f-zhuk/Gear-indicator/Headunit/SW_Headunit/ST7735/ST7735.c

#include "ST7735.h"

#include <limits.h>

#include "main.h"

enum ST7735_STATE_ENUM
{
  ST7735_IDLE,
  ST7735_REDRAW
};

uint8_t _st7735_state = ST7735_IDLE;
uint8_t _colstart = 0;   ///< Some displays need this changed to offset
uint8_t _rowstart = 0;   ///< Some displays need this changed to offset
uint8_t _xstart = 0;
uint8_t _ystart = 0;
uint8_t _height = 0;
uint8_t _width = 0;

bool redraw_busy = false;
uint8_t _redraw_xstart = 0;
uint8_t _redraw_ystart = 0;
uint8_t _redraw_xstop = 0;
uint8_t _redraw_ystop = 0;
uint16_t* _redraw_palette;

// Regular grayscale
const uint16_t st7735_palette[16] = 
{
  0x0000,
  0x0111,
  0x0222,
  0x0333,
  0x0444,
  0x0555,
  0x0666,
  0x0777,
  0x0888,
  0x0999,
  0x0AAA,
  0x0BBB,
  0x0CCC,
  0x0DDD,
  0x0EEE,
  0x0FFF
};

const uint16_t st7735_palette_red[16] = 
{
  0x0000,
  0x0100,
  0x0200,
  0x0300,
  0x0400,
  0x0500,
  0x0600,
  0x0700,
  0x0800,
  0x0811,
  0x0911,
  0x0A21,
  0x0B21,
  0x0C22,
  0x0D22,
  0x0E32
};

const uint16_t st7735_palette_green[16] = 
{
  0x0000,
  0x0111,
  0x0222,
  0x0333,
  0x0444,
  0x0555,
  0x0666,
  0x0777,
  0x0888,
  0x0999,
  0x0AAA,
  0x0BBB,
  0x0CCC,
  0x0DDD,
  0x0EEE,
  0x0FFF
};

const uint16_t st7735_palette_rgbi[16] = 
{
  0x0000,
  0x000A,
  0x00A0,
  0x00AA,
  0x0A00,
  0x0A0A,
  0x0A50,
  0x0AAA,
  0x0555,
  0x055F,
  0x05F5,
  0x05FF,
  0x0F55,
  0x0F5F,
  0x0FF5,
  0x0FFF
};

uint8_t st7735_buffer[ST7735_BUFFER];

SPI_HandleTypeDef *ST7735_SPI;

// SCREEN INITIALIZATION ***************************************************

static const uint8_t Rcmd1[] = {                       // 7735R init, part 1 (red or green tab)
    15,                             // 15 commands in list:
    ST77XX_SWRESET,   ST_CMD_DELAY, //  1: Software reset, 0 args, w/delay
      150,                          //     150 ms delay
    ST77XX_SLPOUT,    ST_CMD_DELAY, //  2: Out of sleep mode, 0 args, w/delay
      255,                          //     500 ms delay
    ST7735_FRMCTR1, 3,              //  3: Framerate ctrl - normal mode, 3 arg:
      0x01, 0x2C, 0x2D,             //     Rate = fosc/(1x2+40) * (LINE+2C+2D)
    ST7735_FRMCTR2, 3,              //  4: Framerate ctrl - idle mode, 3 args:
      0x01, 0x2C, 0x2D,             //     Rate = fosc/(1x2+40) * (LINE+2C+2D)
    ST7735_FRMCTR3, 6,              //  5: Framerate - partial mode, 6 args:
      0x01, 0x2C, 0x2D,             //     Dot inversion mode
      0x01, 0x2C, 0x2D,             //     Line inversion mode
    ST7735_INVCTR,  1,              //  6: Display inversion ctrl, 1 arg:
      0x07,                         //     No inversion
    ST7735_PWCTR1,  3,              //  7: Power control, 3 args, no delay:
      0xA2,
      0x02,                         //     -4.6V
      0x84,                         //     AUTO mode
    ST7735_PWCTR2,  1,              //  8: Power control, 1 arg, no delay:
      0xC5,                         //     VGH25=2.4C VGSEL=-10 VGH=3 * AVDD
    ST7735_PWCTR3,  2,              //  9: Power control, 2 args, no delay:
      0x0A,                         //     Opamp current small
      0x00,                         //     Boost frequency
    ST7735_PWCTR4,  2,              // 10: Power control, 2 args, no delay:
      0x8A,                         //     BCLK/2,
      0x2A,                         //     opamp current small & medium low
    ST7735_PWCTR5,  2,              // 11: Power control, 2 args, no delay:
      0x8A, 0xEE,
    ST7735_VMCTR1,  1,              // 12: Power control, 1 arg, no delay:
      0x0E,
    ST77XX_INVOFF,  0,              // 13: Don't invert display, no args
    ST77XX_MADCTL,  1,              // 14: Mem access ctl (directions), 1 arg:
      0xC8,                         //     row/col addr, bottom-top refresh
    ST77XX_COLMOD,  1,              // 15: set color mode, 1 arg, no delay:
      0x03 };                       //     16-bit color

static const uint8_t Rcmd2green160x80[] = {            // 7735R init, part 2 (mini 160x80)
    2,                              //  2 commands in list:
    ST77XX_CASET,   4,              //  1: Column addr set, 4 args, no delay:
      0x00, ST7735_XOFFSET,                   //     XSTART = 26
      0x00, ST7735_WIDTH-1+ST7735_XOFFSET,      //     XEND = 79
    ST77XX_RASET,   4,              //  2: Row addr set, 4 args, no delay:
      0x00, ST7735_YOFFSET,                   //     XSTART = 0
      0x00, ST7735_HEIGHT-1+ST7735_YOFFSET };   //     XEND = 159

static const uint8_t Rcmd3[] = {                       // 7735R init, part 3 (red or green tab)
    4,                              //  4 commands in list:
    ST7735_GMCTRP1, 16      ,       //  1: Gamma Adjustments (pos. polarity), 16 args + delay:
      0x02, 0x1c, 0x07, 0x12,       //     (Not entirely necessary, but provides
      0x37, 0x32, 0x29, 0x2d,       //      accurate colors)
      0x29, 0x25, 0x2B, 0x39,
      0x00, 0x01, 0x03, 0x10,
    ST7735_GMCTRN1, 16      ,       //  2: Gamma Adjustments (neg. polarity), 16 args + delay:
      0x03, 0x1d, 0x07, 0x06,       //     (Not entirely necessary, but provides
      0x2E, 0x2C, 0x29, 0x2D,       //      accurate colors)
      0x2E, 0x2E, 0x37, 0x3F,
      0x00, 0x00, 0x02, 0x10,
    ST77XX_NORON,     ST_CMD_DELAY, //  3: Normal display on, no args, w/delay
      10,                           //     10 ms delay
    ST77XX_DISPOFF,    ST_CMD_DELAY, //  4: Main screen turn on, no args w/delay
      100 };                        //     100 ms delay

void sendCallback(SPI_HandleTypeDef *hspi)
{
  static uint8_t st7735_linebuffer[ST7735_WIDTH*3/2];
  static uint8_t column = 0;
  static uint8_t line = 0;
  static uint16_t bitcounter = 0;
  uint16_t color = 0;

  if(line > _redraw_ystop)
  {
    line = 0;
    column = 0;
    bitcounter = 0;
    HAL_GPIO_WritePin(ST7735_CS_PIN, GPIO_PIN_SET);
    redraw_busy = false;
    return;
  }
  if(line == 0)
  {
    column = _redraw_xstart;
    line = _redraw_ystart;
  }

  HAL_GPIO_WritePin(ST7735_DC_PIN, GPIO_PIN_SET);

  while((bitcounter<960) && (line<=_redraw_ystop)) // Filling 120-byte buffer
  {
    color = _redraw_palette[( st7735_buffer[(line*ST7735_WIDTH+column)>>1] >> ((~(line*ST7735_WIDTH+column)&1)<<2) )&0x0F]; // each byte contains info about 2 pixels, so index increments twice as slow. Checking high nibble first
    st7735_linebuffer[bitcounter>>3]      &= 0xF00>>(bitcounter&0x04); // no shift for even, >>4 for odd
    st7735_linebuffer[(bitcounter>>3)+1]  &= 0x00F>>(bitcounter&0x04); // no shift for even, >>4 for odd

    if (bitcounter&0x07)
    {
      st7735_linebuffer[bitcounter>>3]      |= color>>8;
      st7735_linebuffer[(bitcounter>>3)+1]  |= color;
    }
    else
    {
      st7735_linebuffer[bitcounter>>3]      |= color>>4;
      st7735_linebuffer[(bitcounter>>3)+1]  |= color<<4;
    }

    bitcounter+=12;
    column++;

    if (column > _redraw_xstop)
    {
      column = _redraw_xstart;
      line++;
    }
  }
  
  HAL_SPI_Transmit_IT(hspi, st7735_linebuffer, bitcounter>>3);
  bitcounter = 0;
}

void sendCommandData(uint8_t cmd, const uint8_t *addr, uint16_t numArgs)
{
  HAL_GPIO_WritePin(ST7735_CS_PIN, GPIO_PIN_RESET);
  HAL_GPIO_WritePin(ST7735_DC_PIN, GPIO_PIN_RESET);
  HAL_SPI_Transmit(ST7735_SPI, &cmd, 1, 100);
  HAL_GPIO_WritePin(ST7735_DC_PIN, GPIO_PIN_SET);
  if(numArgs)
  {
    HAL_GPIO_WritePin(ST7735_DC_PIN, GPIO_PIN_SET);
    HAL_SPI_Transmit(ST7735_SPI, addr, numArgs, 100); //Sending in Interrupt mode
  }
  HAL_GPIO_WritePin(ST7735_DC_PIN, GPIO_PIN_SET);
  HAL_GPIO_WritePin(ST7735_CS_PIN, GPIO_PIN_SET);
}

void sendCommand(uint8_t cmd)
{
  HAL_GPIO_WritePin(ST7735_CS_PIN, GPIO_PIN_RESET);
  HAL_GPIO_WritePin(ST7735_DC_PIN, GPIO_PIN_RESET);
  HAL_SPI_Transmit(ST7735_SPI, &cmd, 1, 100);
  HAL_GPIO_WritePin(ST7735_DC_PIN, GPIO_PIN_SET);
  HAL_GPIO_WritePin(ST7735_CS_PIN, GPIO_PIN_SET);
}

void redraw(void)
{
  redraw_busy = true;
  _redraw_xstart = 0;
  _redraw_ystart = 0;
  _redraw_xstop = _width-1;
  _redraw_ystop = _height-1;
  _redraw_palette = (uint16_t*)&st7735_palette;
  setAddrWindow(0, 0, ST7735_WIDTH, ST7735_HEIGHT);
  uint8_t cmd = ST77XX_RAMWR;
  HAL_GPIO_WritePin(ST7735_CS_PIN, GPIO_PIN_RESET);
  HAL_GPIO_WritePin(ST7735_DC_PIN, GPIO_PIN_RESET);
  HAL_SPI_Transmit_IT(ST7735_SPI, &cmd, 1);
  HAL_GPIO_WritePin(ST7735_DC_PIN, GPIO_PIN_SET);
}

void redraw_partial(uint8_t x, uint8_t y, uint8_t w, uint8_t h, uint16_t* palette)
{
  redraw_busy = true;
  _redraw_xstart = x;
  _redraw_ystart = y;
  _redraw_xstop = x+w-1;
  _redraw_ystop = y+h-1;
  _redraw_palette = palette;

  setAddrWindow(x, y, w, h);
  uint8_t cmd  = ST77XX_RAMWR;
  HAL_GPIO_WritePin(ST7735_CS_PIN, GPIO_PIN_RESET);
  HAL_GPIO_WritePin(ST7735_DC_PIN, GPIO_PIN_RESET);
  HAL_SPI_Transmit_IT(ST7735_SPI, &cmd, 1);
  HAL_GPIO_WritePin(ST7735_DC_PIN, GPIO_PIN_SET);
}

/**************************************************************************/
/*!
    @brief  Companion code to the initiliazation tables. Reads and issues
            a series of LCD commands stored in PROGMEM byte array.
    @param  addr  Flash memory array with commands and data to send
*/
/**************************************************************************/

void ST77XX_sendInitSequence(const uint8_t *addr) {

  uint8_t numCommands, cmd, numArgs;
  uint16_t ms;

  numCommands = *(addr++); // Number of commands to follow
  while (numCommands--) {              // For each command...
    cmd = *(addr++);       // Read command
    numArgs = *(addr++);   // Number of args to follow
    ms = numArgs & ST_CMD_DELAY;       // If hibit set, delay follows args
    numArgs &= ~ST_CMD_DELAY;          // Mask out delay bit
    sendCommandData(cmd, addr, numArgs);
    addr += numArgs;

    if (ms) {
      ms = *(addr++); // Read post-command delay time (ms)
      if (ms == 255)
        ms = 500; // If 255, delay for 500 ms
      HAL_Delay(ms);
    }
  }
}

/**************************************************************************/
/*!
  @brief  SPI displays set an address window rectangle for blitting pixels
  @param  x  Top left corner x coordinate
  @param  y  Top left corner y coordinate
  @param  w  Width of window
  @param  h  Height of window
*/
/**************************************************************************/
void setAddrWindow(uint8_t x, uint8_t y, uint8_t w, uint8_t h) {
  uint8_t BufferX [4] = {0x00, ST7735_XOFFSET+x, 0x00, (ST7735_XOFFSET+x+w-1)};
  sendCommandData(ST77XX_CASET, BufferX, 4); // Column addr set
  uint8_t BufferY [4] = {0x00, ST7735_YOFFSET+y, 0x00, (ST7735_YOFFSET+y+h-1)};
  sendCommandData(ST77XX_RASET, BufferY, 4);// Row addr set
  //SPI_WRITE32(ya);

  //writeCommand(ST77XX_RAMWR); // write to RAM
}

/**************************************************************************/
/*!
    @brief  Set origin of (0,0) of display with offsets
    @param  col  The offset from 0 for the column address
    @param  row  The offset from 0 for the row address
*/
/**************************************************************************/
void setColRowStart(int8_t col, int8_t row) {
  _colstart = col;
  _rowstart = row;
}

/**************************************************************************/
/*!
    @brief  Set origin of (0,0) of display with offsets
*/
/**************************************************************************/
uint8_t* getBufferPointer(void) {
  return (uint8_t*)&st7735_buffer;
}

/**************************************************************************/
/*!
 @brief  Change whether display is on or off
 @param  enable True if you want the display ON, false OFF
 */
/**************************************************************************/
void enableDisplay(bool enable) {
  sendCommand(enable ? ST77XX_DISPON : ST77XX_DISPOFF);
}

/**************************************************************************/
/*!
 @brief  Change whether TE pin output is on or off
 @param  enable True if you want the TE pin ON, false OFF
 */
/**************************************************************************/
void enableTearing(bool enable) {
  sendCommand(enable ? ST77XX_TEON : ST77XX_TEOFF);
}

/**************************************************************************/
/*!@yadrenbaton13
 @brief  Change whether sleep mode is on or off
 @param  enable True if you want sleep mode ON, false OFF
 */
/**************************************************************************/
void enableSleep(bool enable) {
  sendCommand(enable ? ST77XX_SLPIN : ST77XX_SLPOUT);
}

/**************************************************************************/
/*!
 @brief  Change whether inverted mode is on or off
 @param  enable True if you want inverted mode ON, false OFF
 */
/**************************************************************************/
void enableInvert(bool enable){
  sendCommand(enable ? ST77XX_INVON : ST77XX_INVOFF);
}

/**************************************************************************/
/*!
    @brief  Initialization code common to all ST7735R displays
    @param  options  Tab color from adafruit purchase
*/
/**************************************************************************/
void initR(SPI_HandleTypeDef *hspi) {
  ST7735_SPI = hspi;

  HAL_SPI_RegisterCallback(ST7735_SPI, HAL_SPI_TX_COMPLETE_CB_ID, sendCallback);

  HAL_GPIO_WritePin(ST7735_RES_PIN, GPIO_PIN_SET);
  HAL_GPIO_WritePin(ST7735_CS_PIN, GPIO_PIN_SET);
  HAL_GPIO_WritePin(ST7735_DC_PIN, GPIO_PIN_SET);
  ST77XX_sendInitSequence(Rcmd1);

  _width = ST7735_WIDTH;
  _height = ST7735_HEIGHT;
  ST77XX_sendInitSequence(Rcmd2green160x80);
  _colstart = 24;
  _rowstart = 0;

  _redraw_xstart = 0;
  _redraw_ystart = 0;
  _redraw_xstop = _width;
  _redraw_ystop = _height;

  ST77XX_sendInitSequence(Rcmd3);

  // Black tab, change MADCTL color filter
  //uint8_t data = 0xC8;
  //sendCommandData(ST77XX_MADCTL, &data, 1); //redundant

  setRotation(0);
}

// OTHER FUNCTIONS *********************************************************

/**************************************************************************/
/*!
    @brief  Set origin of (0,0) and orientation of TFT display
    @param  m  The index for rotation, from 0-3 inclusive
*/
/**************************************************************************/
void setRotation(uint8_t m) {
  uint8_t madctl = ST7735_MADCTL_BGR;

  uint8_t rotation = m & 3; // can't be higher than 3

  switch (rotation) {
  case 0:
    
    madctl |= ST77XX_MADCTL_MX | ST77XX_MADCTL_MY;
    
    _height = ST7735_HEIGHT;
    _width = ST7735_WIDTH;
    _xstart = _colstart;
    _ystart = _rowstart;
    break;
  case 1:

    madctl |= ST77XX_MADCTL_MY | ST77XX_MADCTL_MV;
    
    _width = ST7735_HEIGHT;
    _height = ST7735_WIDTH;
    _ystart = _colstart;
    _xstart = _rowstart;
    break;
  case 2:
    _height = ST7735_HEIGHT;
    _width = ST7735_WIDTH;
    _xstart = _colstart;
    _ystart = _rowstart;
    break;
  case 3:
  
    madctl |= ST77XX_MADCTL_MX | ST77XX_MADCTL_MV;

    _width = ST7735_HEIGHT;
    _height = ST7735_WIDTH;
    _ystart = _colstart;
    _xstart = _rowstart;
    break;
  }

  sendCommandData(ST77XX_MADCTL, &madctl, 1);
}
