f-zhuk/Gear-indicator/Headunit/SW_Headunit/Core/Src/display.c

/**
 * @file display.c
 *
 */

/*********************
 *      INCLUDES
 *********************/

#include "display.h"

/*********************
 *      DEFINES
 *********************/

/**********************
 *      TYPEDEFS
 **********************/

/**********************
 *  STATIC PROTOTYPES
 **********************/

/**********************
 *  STATIC VARIABLES
 **********************/

/**********************
 *  VARIABLES
 **********************/

 display_descriptor display;

/**********************
 * GLOBAL PROTOTYPES
 **********************/

/**********************
 *      MACROS
 **********************/

/**********************
 *   GLOBAL FUNCTIONS
 **********************/

void setCursor(float x, float y)
{
    display.xcursor = x;
    display.ycursor = y;
}

void putChar(uint8_t character, font_t font, uint8_t color) // color used only for 1bpp fonts
{
    uint8_t cmap = 0;
    character -= (font.cmaps[cmap].range_start - font.cmaps[cmap].glyph_id_start);
    uint32_t bmi = font.glyph_dsc[character].bitmap_index; //Bitmap index
    uint8_t * bm = font.glyph_bitmap;  // Bitmap

    int16_t xstart = (int16_t)display.xcursor+font.glyph_dsc[character].ofs_x;
    int16_t ystart = (int16_t)display.ycursor-font.glyph_dsc[character].ofs_y+font.base_line-font.glyph_dsc[character].box_h;

    int16_t box_w = font.glyph_dsc[character].box_w;
    if(xstart+box_w>display.width) // Check right
        box_w = display.width-xstart;
    int16_t box_h = font.glyph_dsc[character].box_h;
    if(ystart+box_h>display.height) // Check bottom
        box_h = display.height-ystart;

    uint16_t i=0;
    if(ystart<0) // Check top
        i = -ystart;
    while (i<box_h)
    {
        uint16_t j=0;
        if(xstart<0) // Check left
            j = -xstart;
        while (j<box_w)
        {
            uint8_t data = 0;
            switch (font.bpp)
            {
                case 4:
                data = (bm[bmi+((i*font.glyph_dsc[character].box_w+j)>>1)] >> ((~(i*font.glyph_dsc[character].box_w+j)&0x01)<<2)) & 0x0F;
                break;

                case 1:
                if ((bm[bmi+((i*font.glyph_dsc[character].box_w+j)>>3)] >> (~(i*font.glyph_dsc[character].box_w+j)&0x07)) & 0x01)
                    data = color&0x0F;
                break;
            }
            
            if(data)
            {
                uint16_t wbi = ((display.width)*(i+ystart)+xstart+j); // Working buffer index
                display.target_buffer[wbi>>1] &= (0x0F<<((wbi&0x01)<<2));
                display.target_buffer[wbi>>1] |=  (data << ((~wbi&0x01)<<2));
            }
            j++;
        }
        i++;
    }
    display.xcursor = xstart+box_w+1;
}


void putString(uint8_t* string, font_t font, uint8_t color) // color used only for 1bpp fonts
{
    while (*string != 0)
    {
        putChar(*string, font, color);
        string++;
    }
}

void putNumber_u8(uint8_t number, font_t font, uint8_t color) // color used only for 1bpp fonts
{
    uint8_t string[4] = {'0'+(number/100)%10, '0'+(number/10)%10, '0'+number%10, 0};
    putString((uint8_t*)&string, font, color);
}

void putNumber_i8(int8_t number, font_t font, uint8_t color) // color used only for 1bpp fonts
{    
    if (number > 0)
    {
        uint8_t string[5] = {'+', '0'+(number/100)%10, '0'+(number/10)%10, '0'+number%10, 0};
        putString((uint8_t*)&string, font, color);
    }
    else if (number < 0)
    {
        uint8_t abs = -number;
        uint8_t string[5] = {'-', '0'+(abs/100)%10, '0'+(abs/10)%10, '0'+abs%10, 0};
        putString((uint8_t*)&string, font, color);
    }
    else
        putChar('0', font, color);
}

void fillRectangle(uint16_t width, uint16_t height, uint8_t color)
{
    color &= 0x0f;

    if ((int16_t)display.xcursor+width > display.width) // Check right
        width = display.width-display.xcursor;
    if ((int16_t)display.ycursor+height > display.height) // Check bottom
        height = display.height-display.ycursor;

    uint16_t i=0;    
    if ((int16_t)display.ycursor < 0) // Check top
        i = -(int16_t)display.ycursor;
    while (i<height)
    {
        uint16_t j=0;
        if ((int16_t)display.xcursor < 0) // Check left
            j = -(int16_t)display.xcursor;
        while (j<width)
        {
            uint16_t wbi = (((display.width)*(i+(int16_t)display.ycursor))+(int16_t)display.xcursor+j); // Working buffer index
            display.target_buffer[wbi>>1] &= (0x0F<<((wbi&0x01)<<2));
            display.target_buffer[wbi>>1] |=  (color << ((~wbi&0x01)<<2));
            j++;
        }
        i++;
    }
    display.xcursor += width;
    display.ycursor += height;
}

void displayInit(uint8_t *target_buffer, uint16_t width, uint16_t height)
{
    display.target_buffer = target_buffer;
    display.width = width;
    display.height = height;
    setCursor(0,0);
    for(uint32_t i = 0; i<(width*height); i++)
        display.target_buffer[i>>1] = (display.target_buffer[i>>1] & (0x0F<<((i&1)<<2))) | (0x00<<((~i&1)<<2));
}

/**********************
 *   STATIC FUNCTIONS
 **********************/
