f-zhuk/Gear-indicator/Headunit/SW_Headunit/Core/Inc/display.h

/**
 * @file display.h
 *
 */

#ifndef DISPLAY_H
#define DISPLAY_H

/*********************
 *      INCLUDES
 *********************/

#include <stdint.h>
#include <stddef.h>
#include "../../Fonts/fonts.h"

/*********************
 *      DEFINES
 *********************/


/**********************
 *      TYPEDEFS
 **********************/

typedef struct {
    uint8_t * target_buffer;    // Pointer to a working buffer
    uint16_t width;              // Working buffer width
    uint16_t height;             // Working buffer height
    float xcursor;
    float ycursor;
} display_descriptor;

/**********************
 * GLOBAL PROTOTYPES
 **********************/

void setCursor(float x, float y);
void putChar(uint8_t character, font_t font, uint8_t color);
void putString(uint8_t* character, font_t font, uint8_t color);
void putNumber_u8(uint8_t number, font_t font, uint8_t color);
void putNumber_i8(int8_t number, font_t font, uint8_t color);
void fillRectangle(uint16_t width, uint16_t height, uint8_t color);
void displayInit(uint8_t * target_buffer, uint16_t width, uint16_t height);

#endif /*DISPLAY_H*/
